pablodietz/microstrip-antenna/images/rl-1.pdf

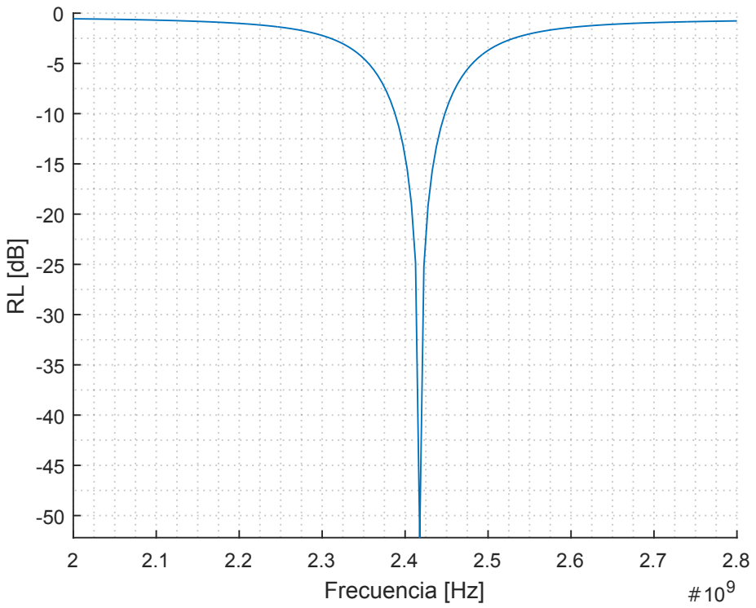
[picture p14: figure]
Frecuencia [Hz]
