pablodietz/microstrip-antenna/images/zin-equivalent-circuit.pdf

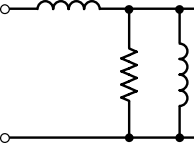
[picture p15: figure]
