pablodietz/microstrip-antenna/images/antenna-finished-2.png

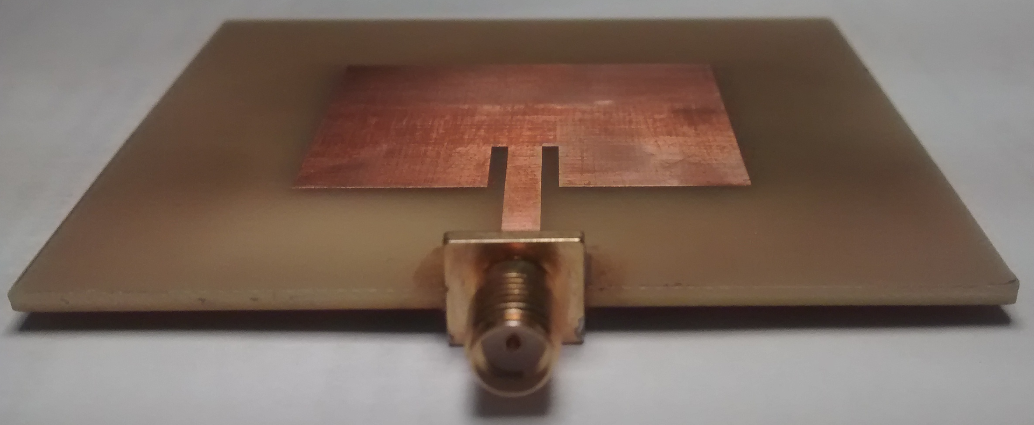
images/antenna-finished-2.png
