pablodietz/microstrip-antenna/images/cad-feko.png

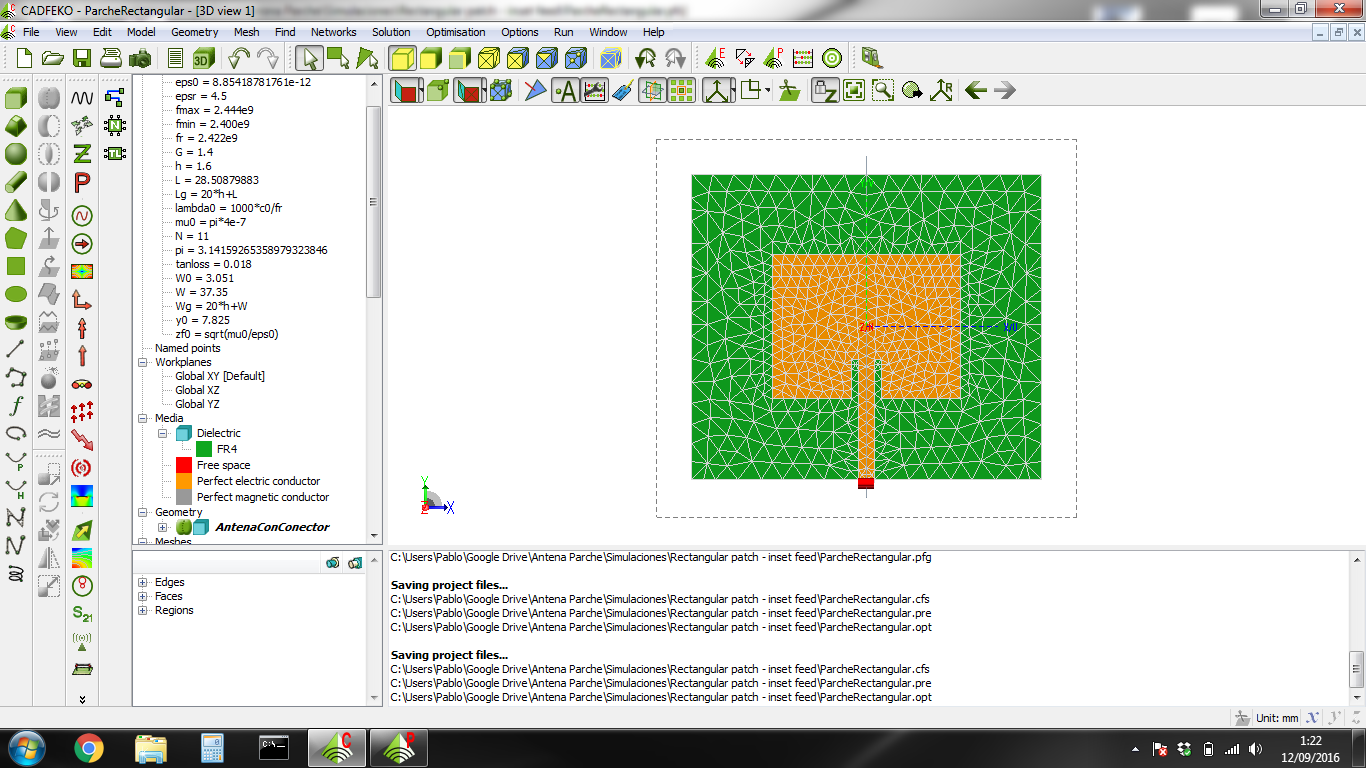
images/cad-feko.png
