pablodietz/microstrip-antenna/images/circuital-model-1.png

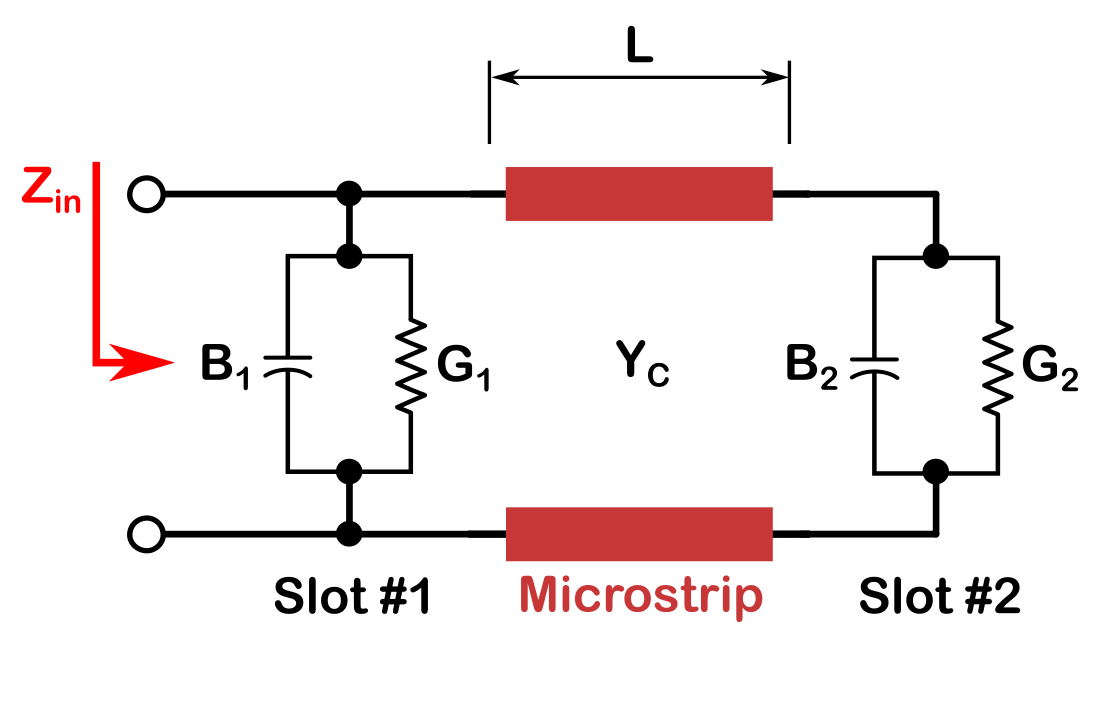
images/circuital-model-1.png
