pablodietz/microstrip-antenna/images/effective-dielectric-constant-formula.png

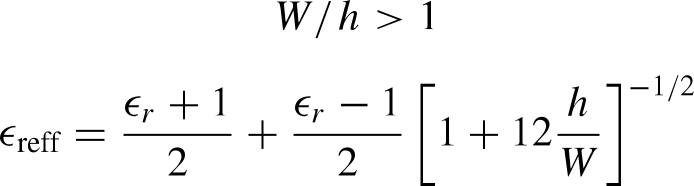
images/effective-dielectric-constant-formula.png
