pablodietz/microstrip-antenna/images/effective-dielectric-constant.png

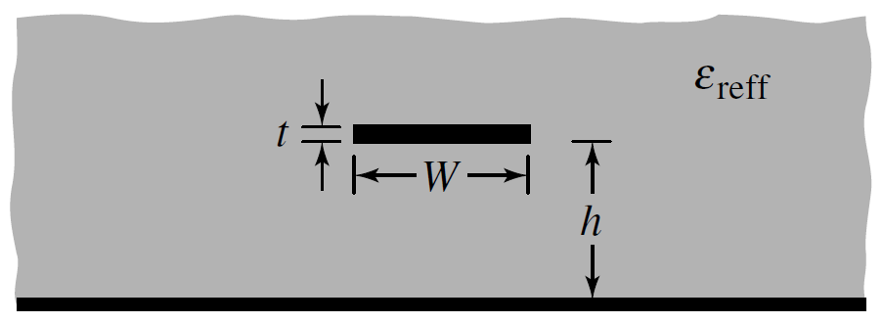
images/effective-dielectric-constant.png
