pablodietz/microstrip-antenna/images/effective-length.png

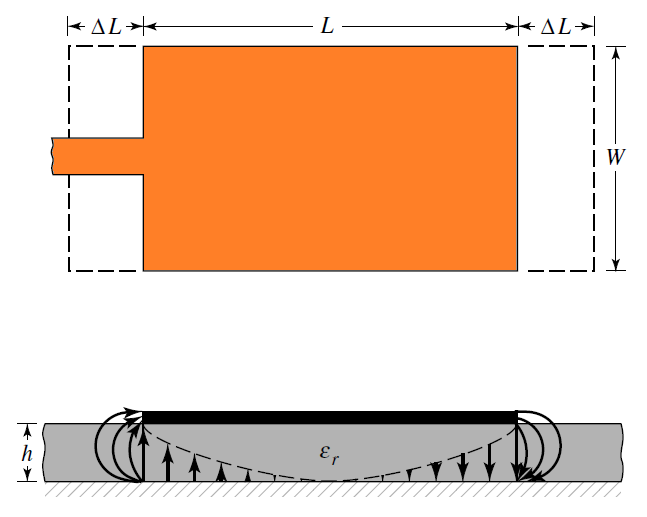
images/effective-length.png
