pablodietz/microstrip-antenna/images/EH-plane.png

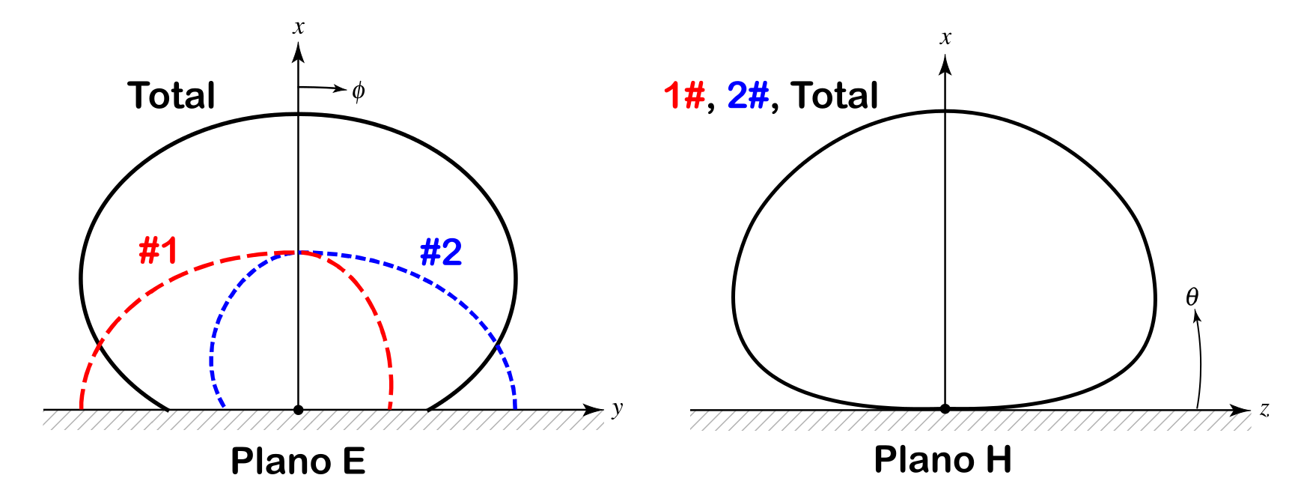
images/EH-plane.png
