pablodietz/microstrip-antenna/images/feeding-3.png

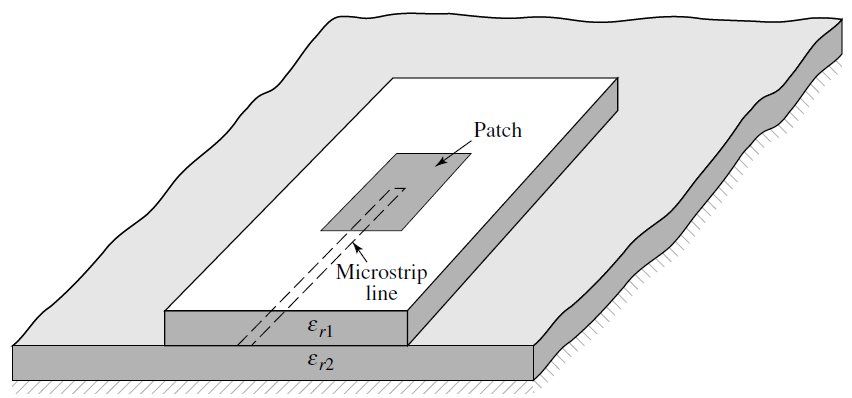
images/feeding-3.png
