pablodietz/microstrip-antenna/images/fringing-effect-1.png

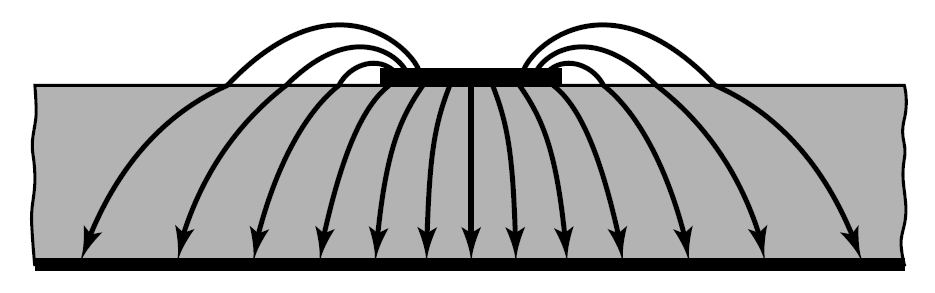
images/fringing-effect-1.png
