pablodietz/microstrip-antenna/images/fringing-effect-2.png

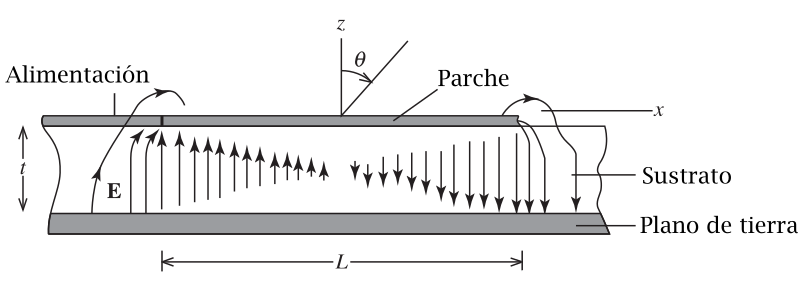
images/fringing-effect-2.png
