pablodietz/microstrip-antenna/images/g1-vs-w.png

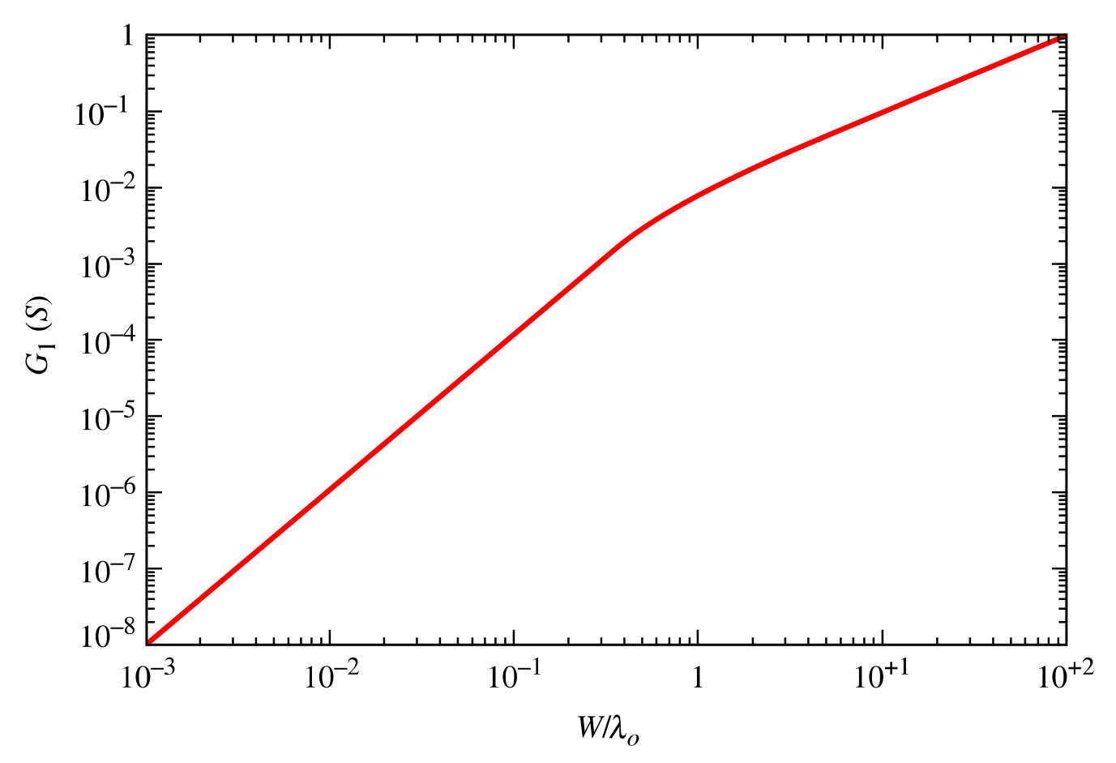
images/g1-vs-w.png
