pablodietz/microstrip-antenna/images/JsMs.png

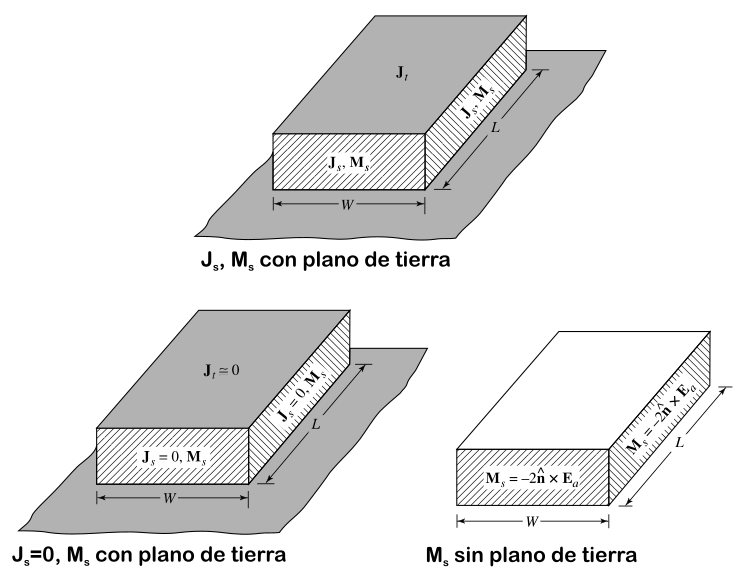
images/JsMs.png
