pablodietz/microstrip-antenna/images/magnetic-current-1.png

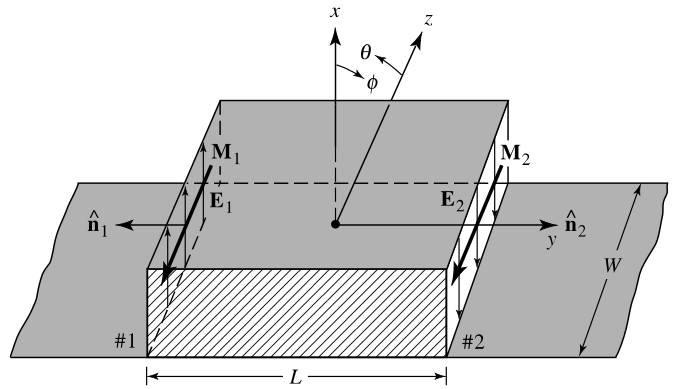
images/magnetic-current-1.png
