pablodietz/microstrip-antenna/images/magnetic-current-2.png

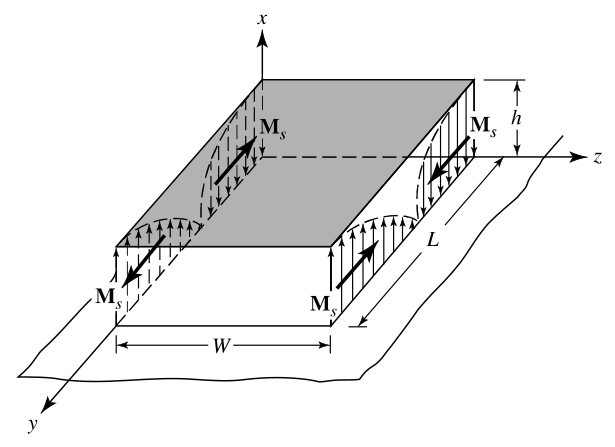
images/magnetic-current-2.png
