pablodietz/microstrip-antenna/images/matching-circuit-1.png

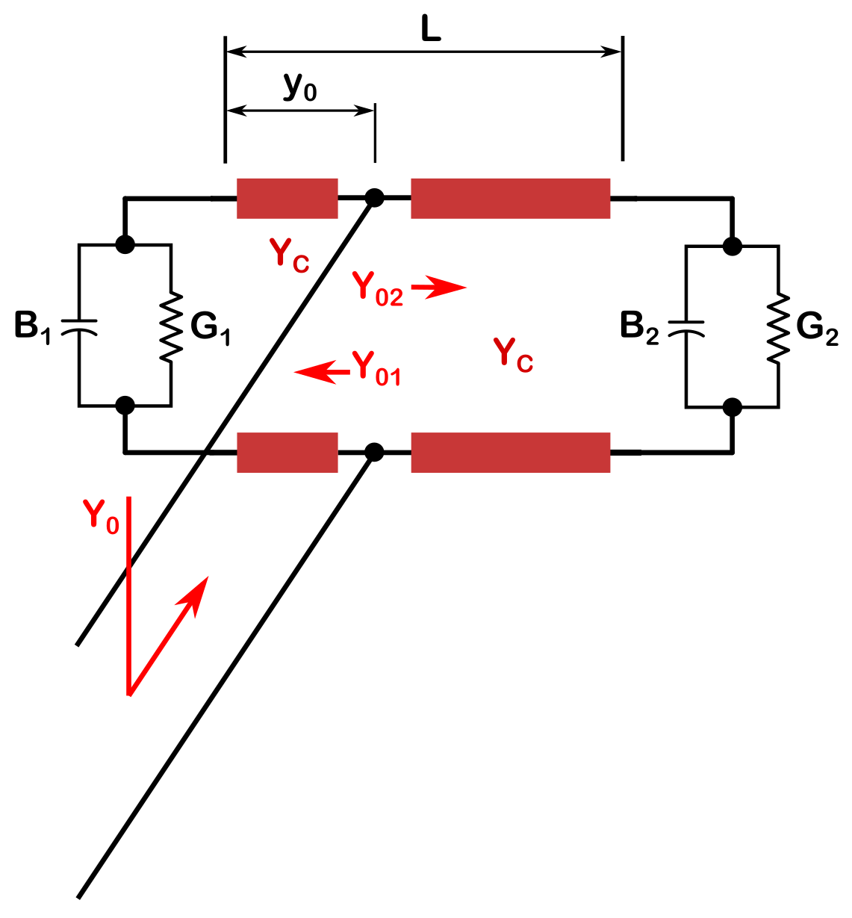
images/matching-circuit-1.png
