pablodietz/microstrip-antenna/images/matching-circuit-2.png

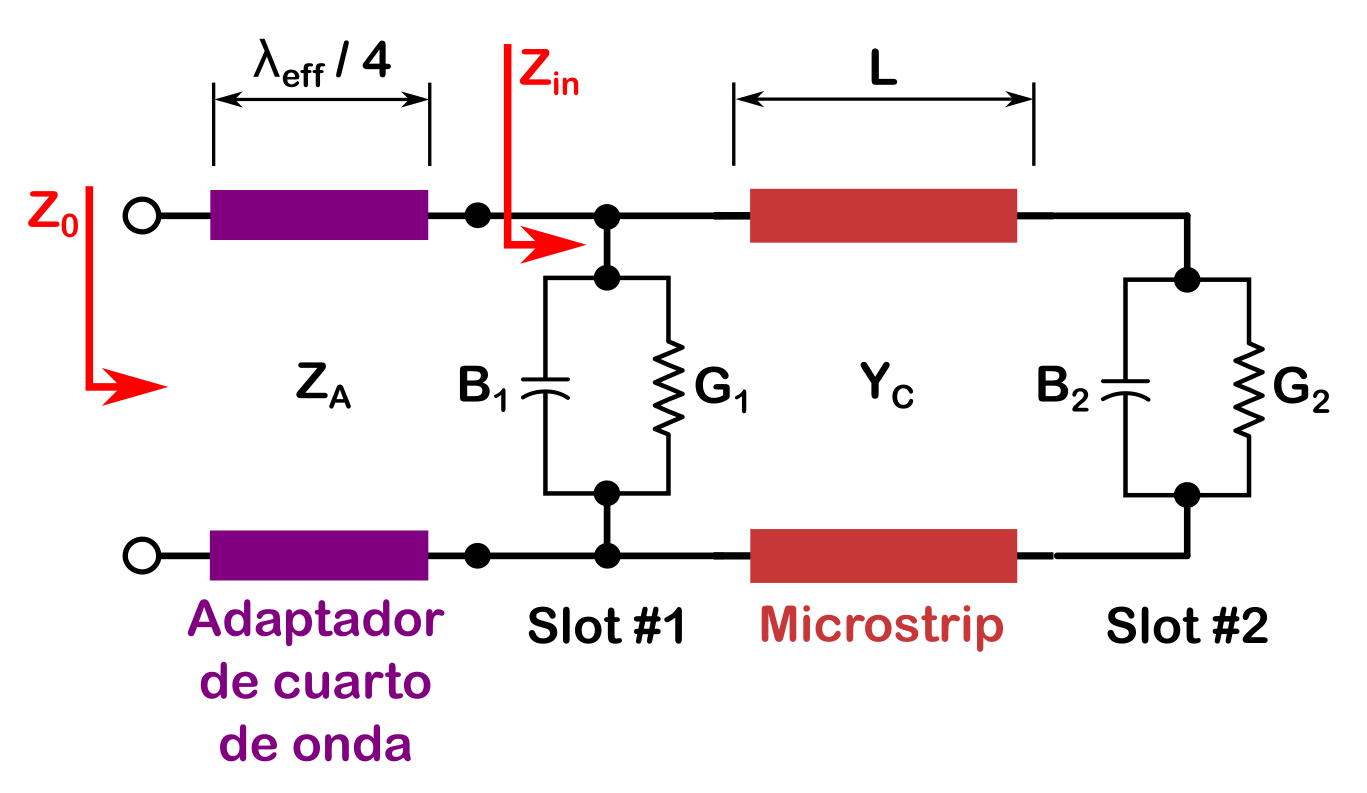
images/matching-circuit-2.png
