pablodietz/microstrip-antenna/images/mesh.png

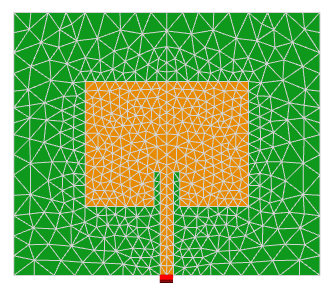
images/mesh.png
