pablodietz/microstrip-antenna/images/microstrip.png

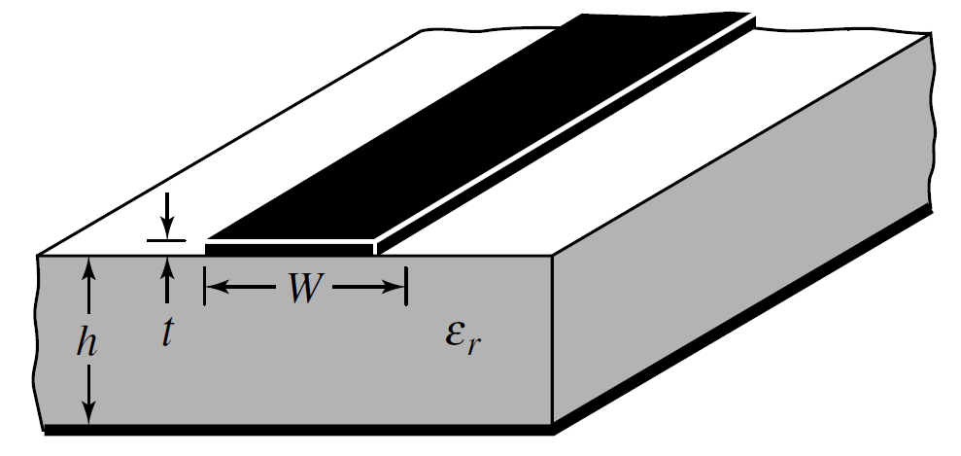
images/microstrip.png
