pablodietz/microstrip-antenna/images/modes.png

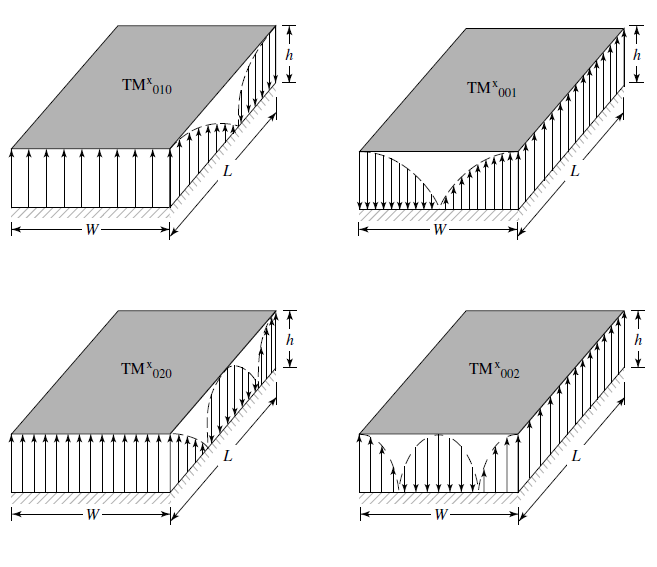
images/modes.png
