pablodietz/microstrip-antenna/images/near-field.png

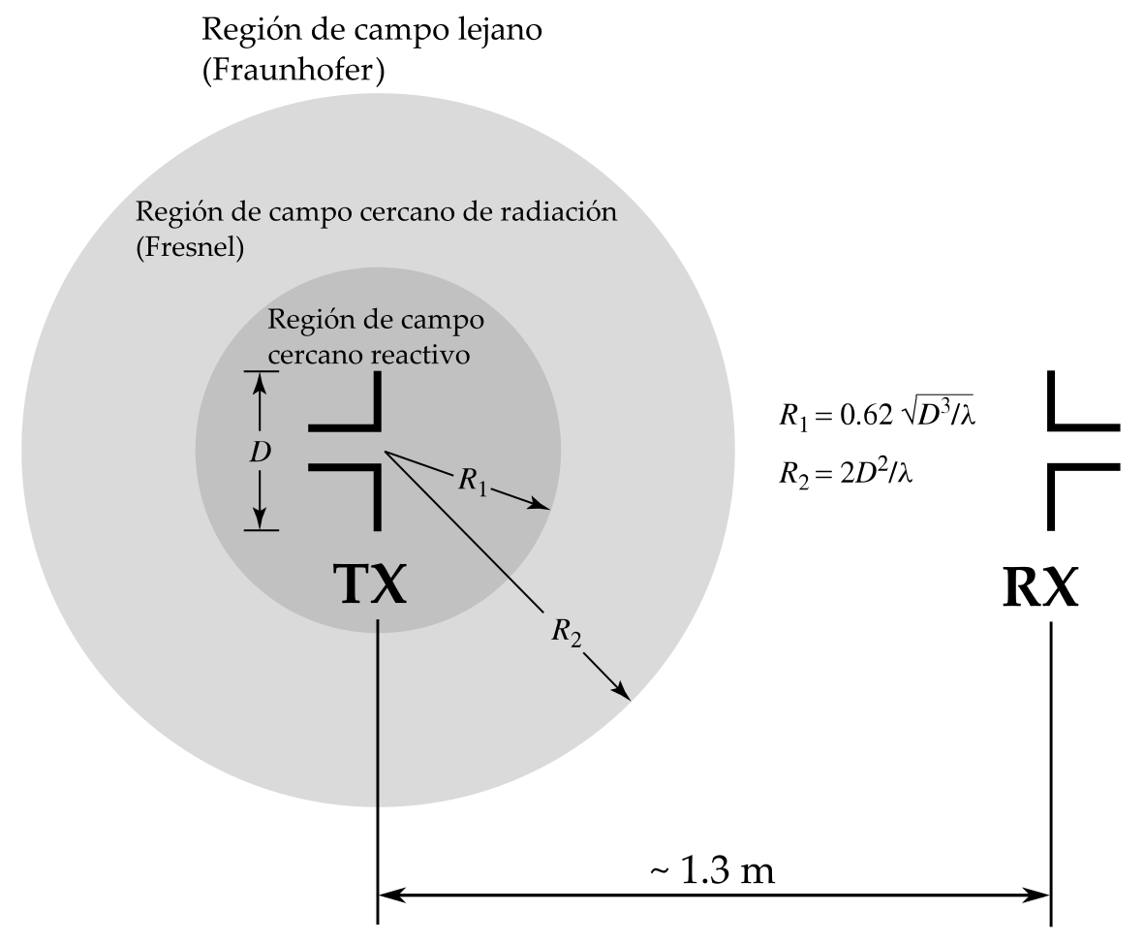
images/near-field.png
