pablodietz/microstrip-antenna/images/patch-types.png

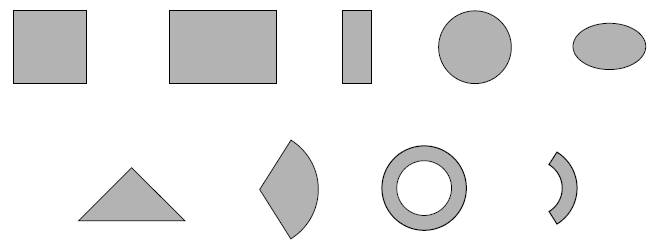
images/patch-types.png
