pablodietz/microstrip-antenna/images/patch.png

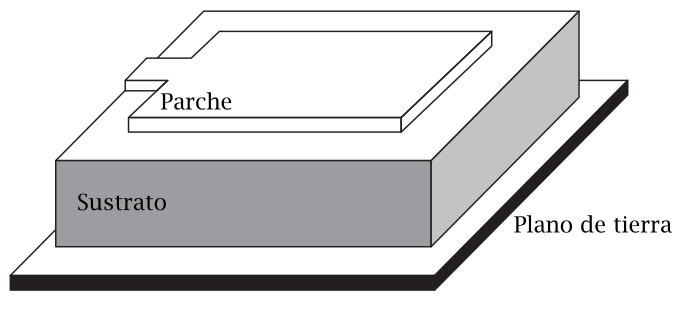
images/patch.png
