pablodietz/microstrip-antenna/images/post-feko.png

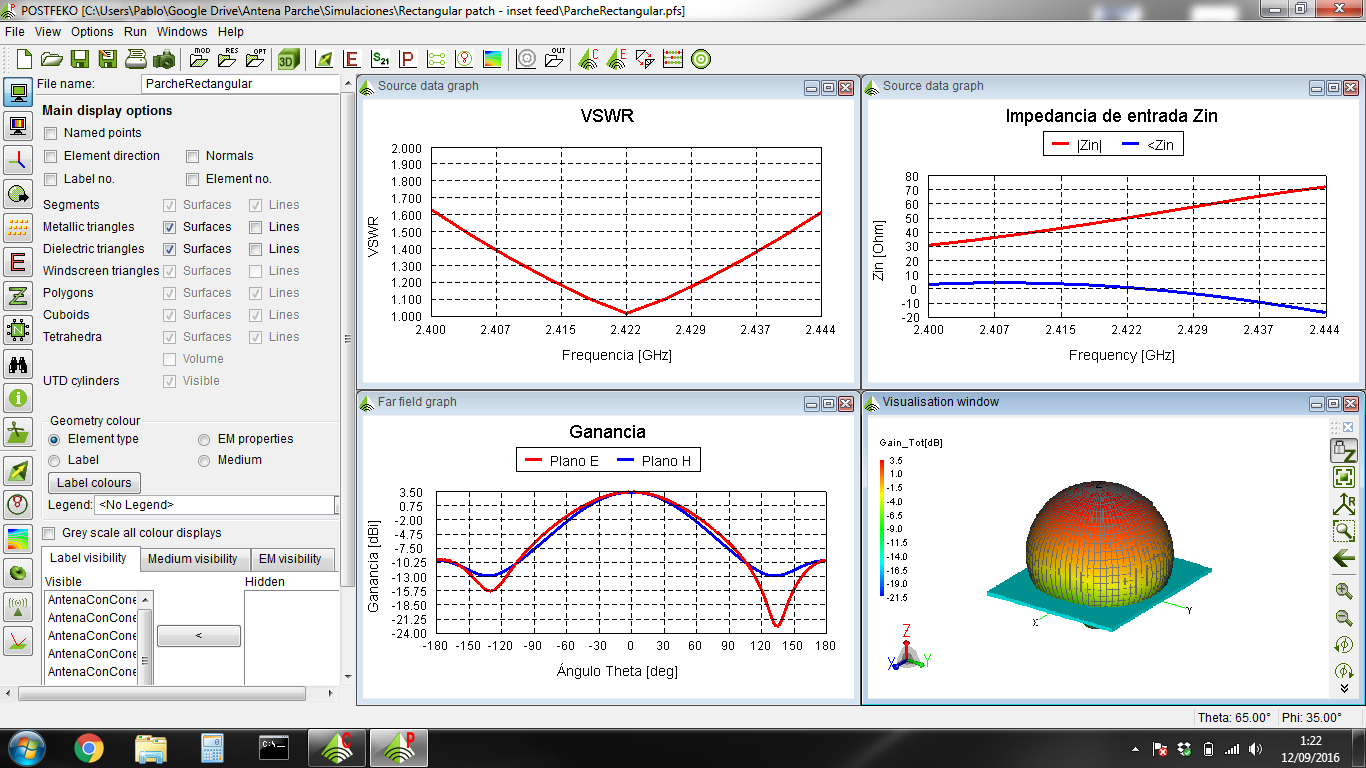
images/post-feko.png
