pablodietz/microstrip-antenna/images/propagation.png

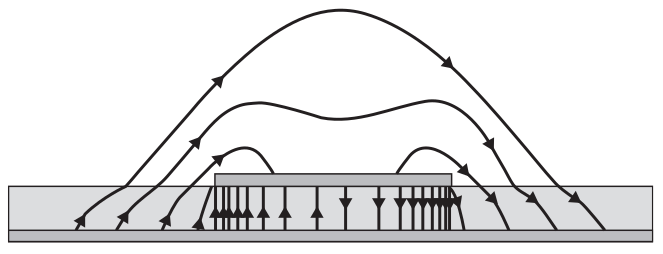
images/propagation.png
