pablodietz/microstrip-antenna/images/rl1.png

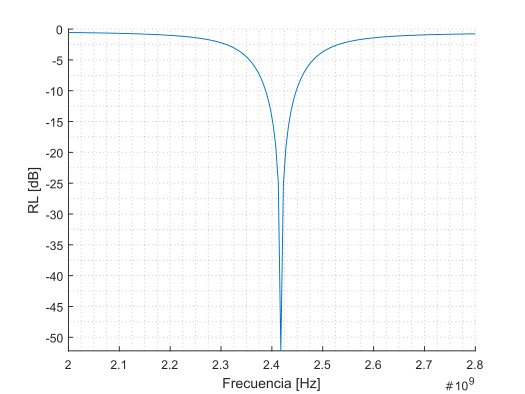
images/rl1.png
