pablodietz/microstrip-antenna/images/rl-2.png

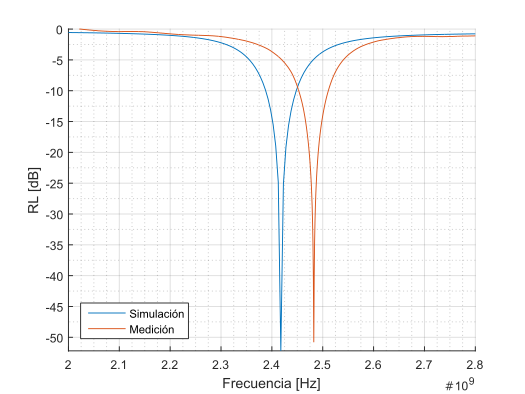
images/rl-2.png
