pablodietz/microstrip-antenna/images/rl-4.png

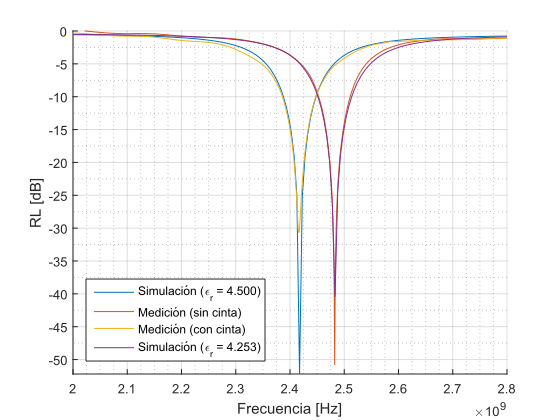
images/rl-4.png
