pablodietz/microstrip-antenna/images/sma-1.jpg

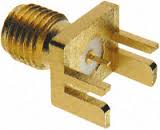
images/sma-1.jpg
