pablodietz/microstrip-antenna/images/sma-2.jpg

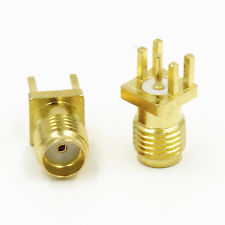
images/sma-2.jpg
