pablodietz/microstrip-antenna/images/smith-model.png

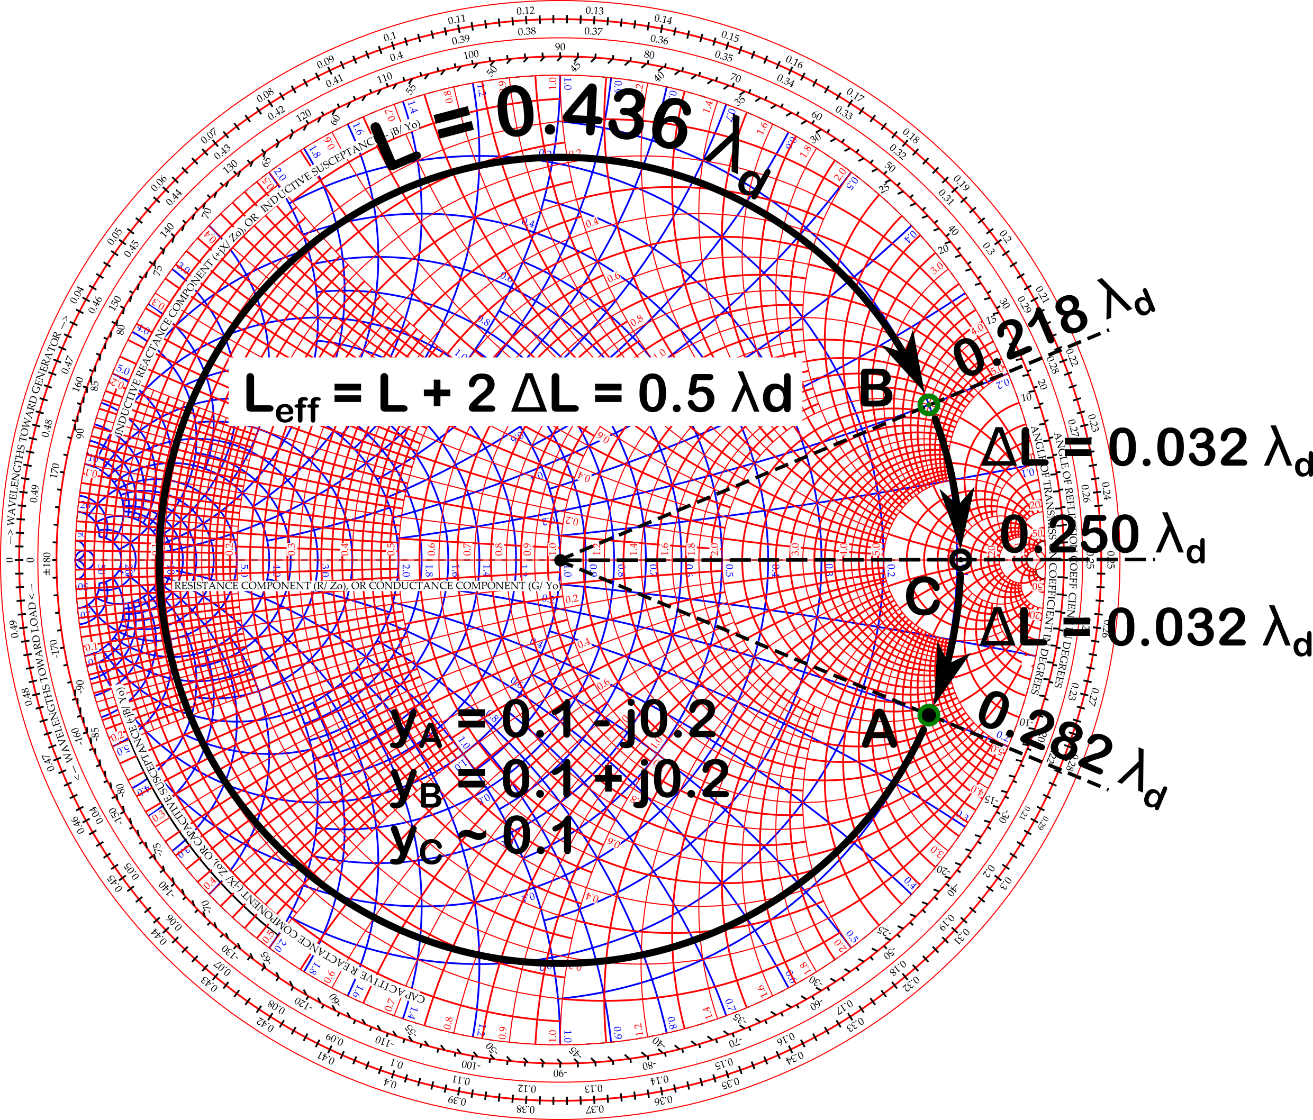
images/smith-model.png
