pablodietz/microstrip-antenna/images/zin-equivalent-circuit.png

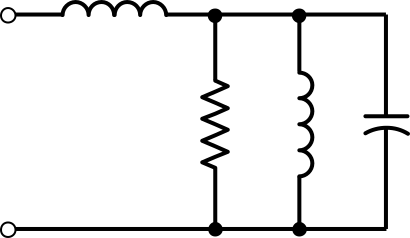
images/zin-equivalent-circuit.png
