pablodietz/microstrip-antenna/images/radiation-pattern-setup.png

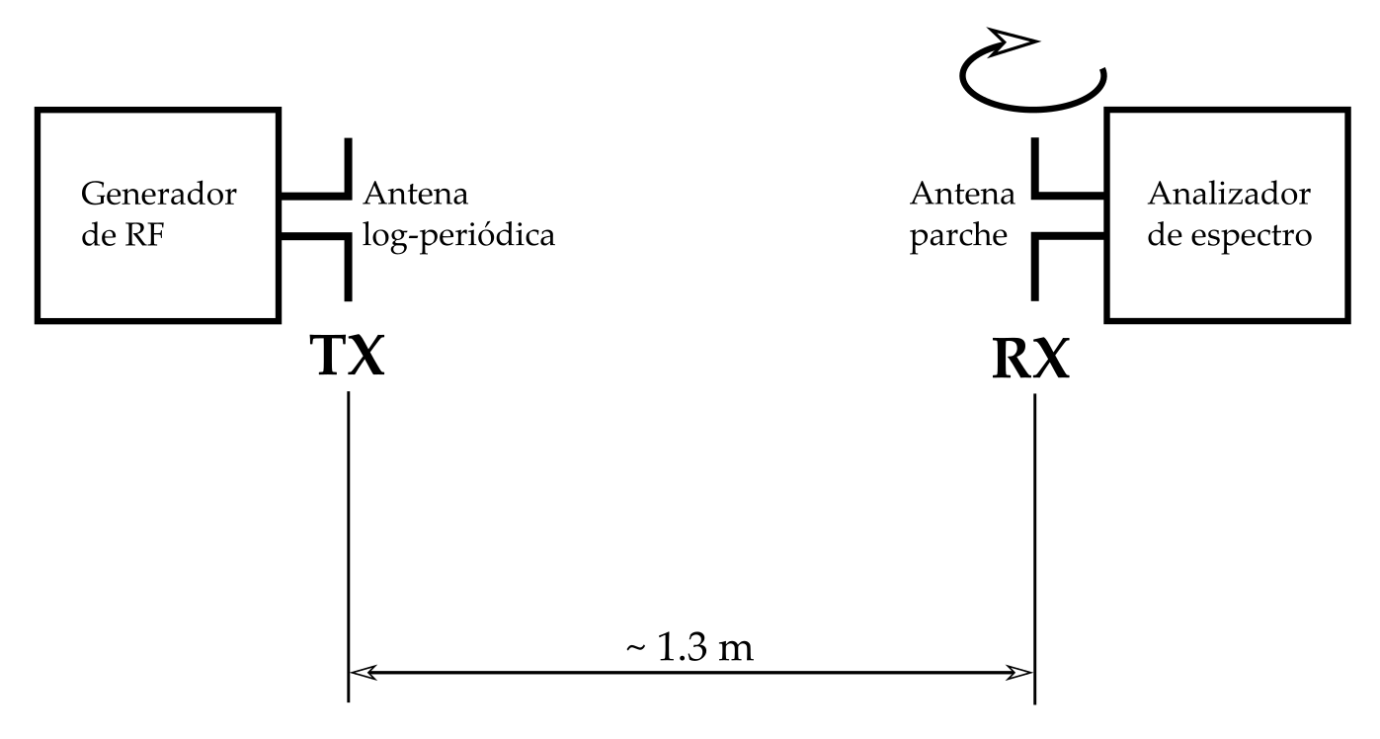
images/radiation-pattern-setup.png
