pablodietz/microstrip-antenna/images/rl-setup.png

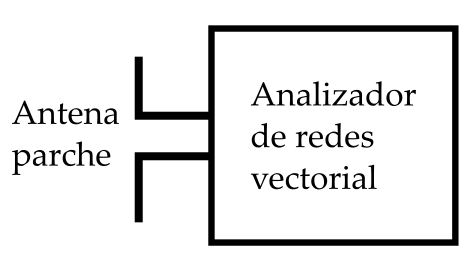
images/rl-setup.png
