pablodietz/microstrip-antenna/images/rl-3.pdf

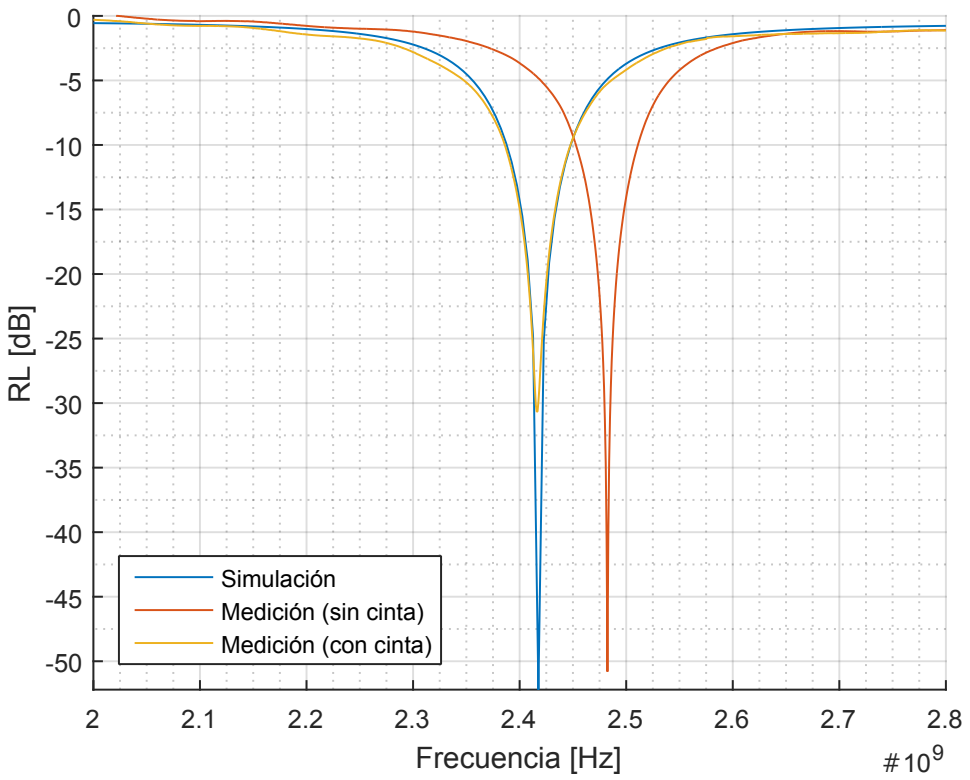
[picture p62: page 1]
Frecuencia [Hz]

Simulación
Medición (sin cinta)
Medición (con cinta)
