pablodietz/microstrip-antenna/images/rl-4.pdf

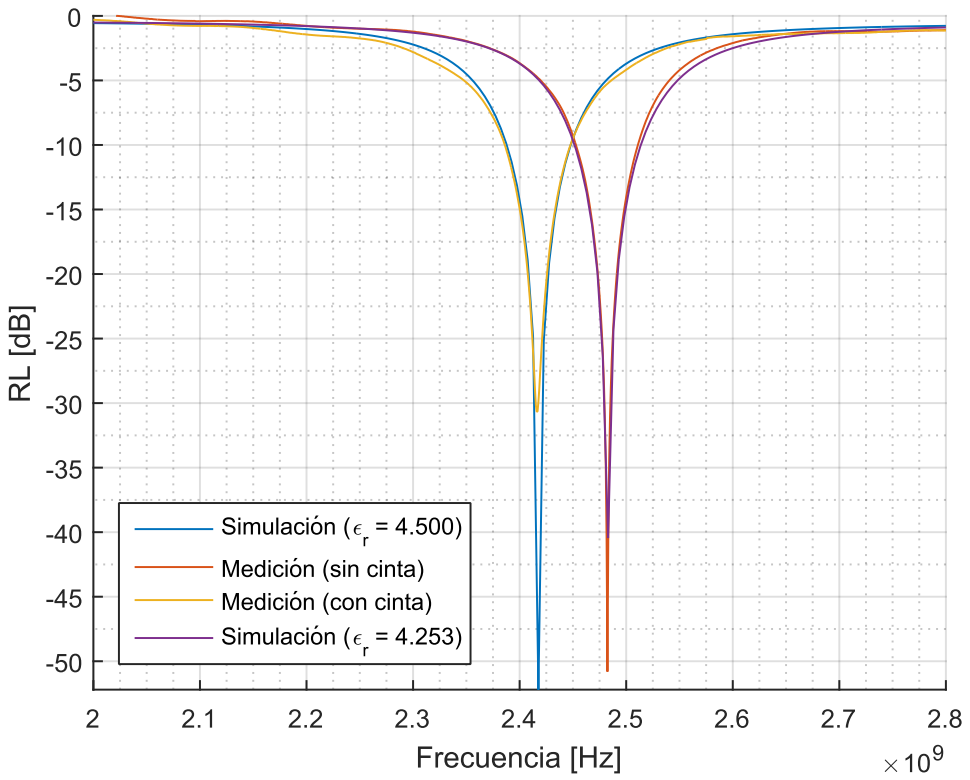
[picture p63: page 1]
