pablodietz/microstrip-antenna/images/rl-5.pdf

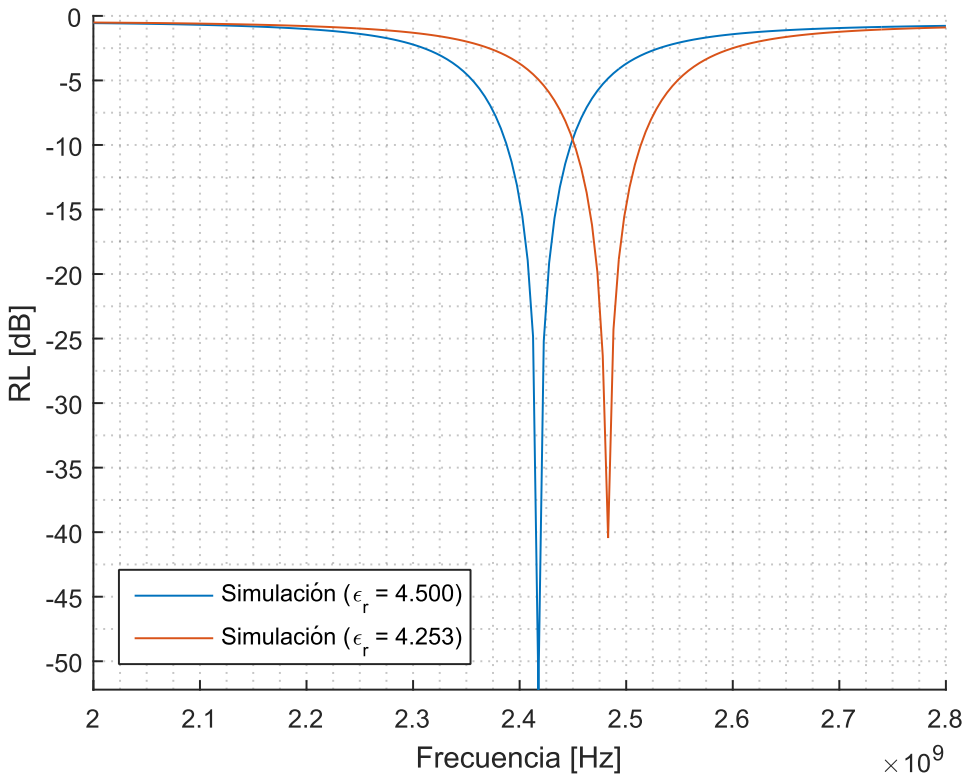
[picture p64: page 1]
