pablodietz/microstrip-antenna/images/rl-6.pdf

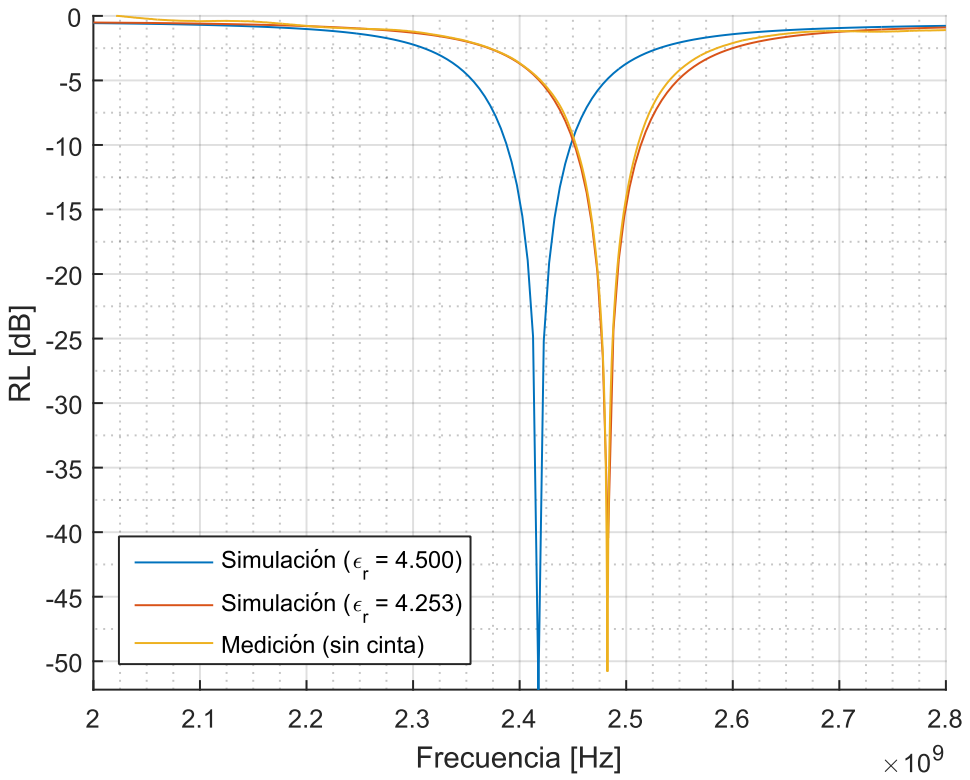
[picture p65: page 1]
