pablodietz/microstrip-antenna/images/rl-7.pdf

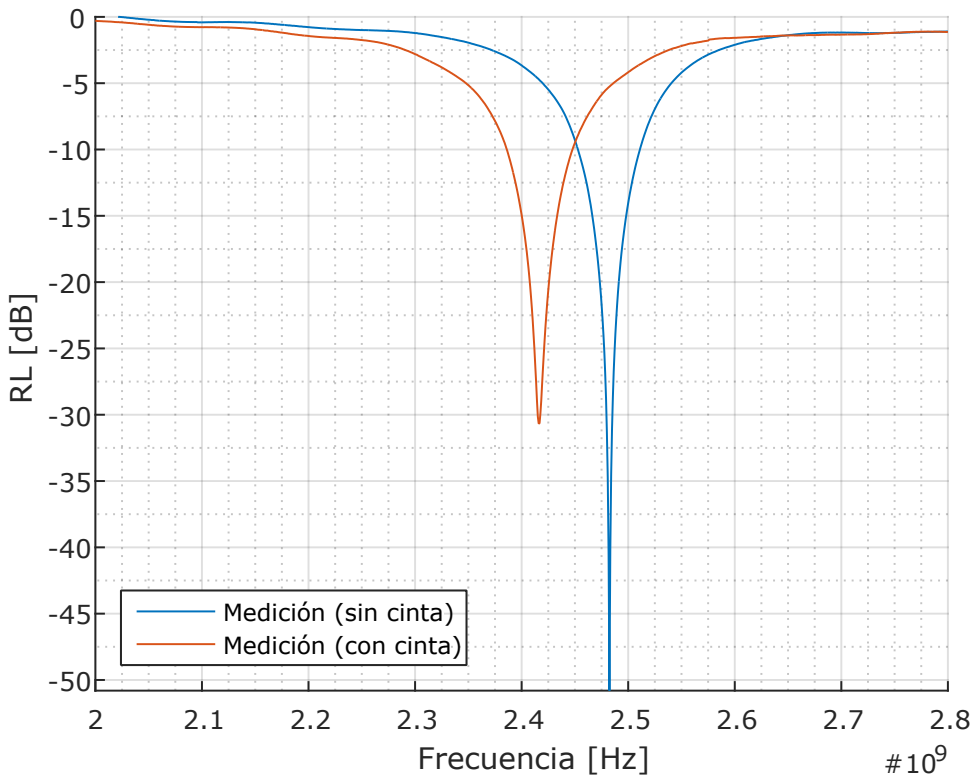
[picture p66: page 1]
Frecuencia [Hz]

Medición (sin cinta)
Medición (con cinta)
