pablodietz/microstrip-antenna/images/rl2.pdf

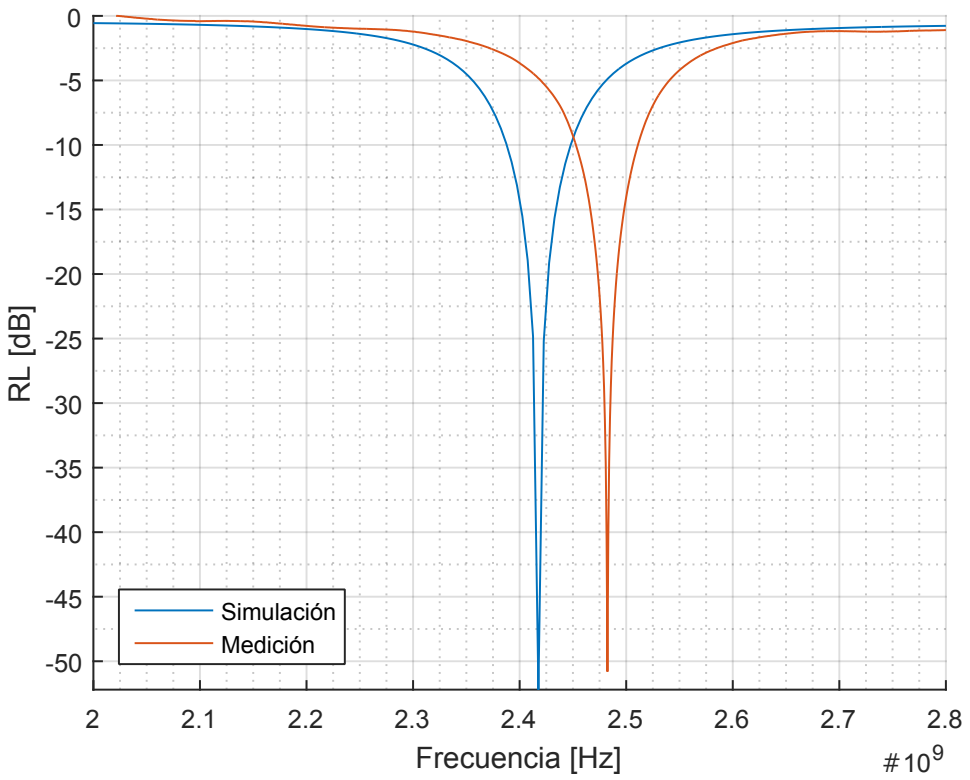
[picture p67: page 1]
Frecuencia [Hz]

Simulación
Medición
